shasradha/Orbit/hardware/Orbit-KiCad-Main/orbit.kicad_sch

## KiCad design hardware/Orbit-KiCad-Main/orbit.kicad_sch (2026-08-10)

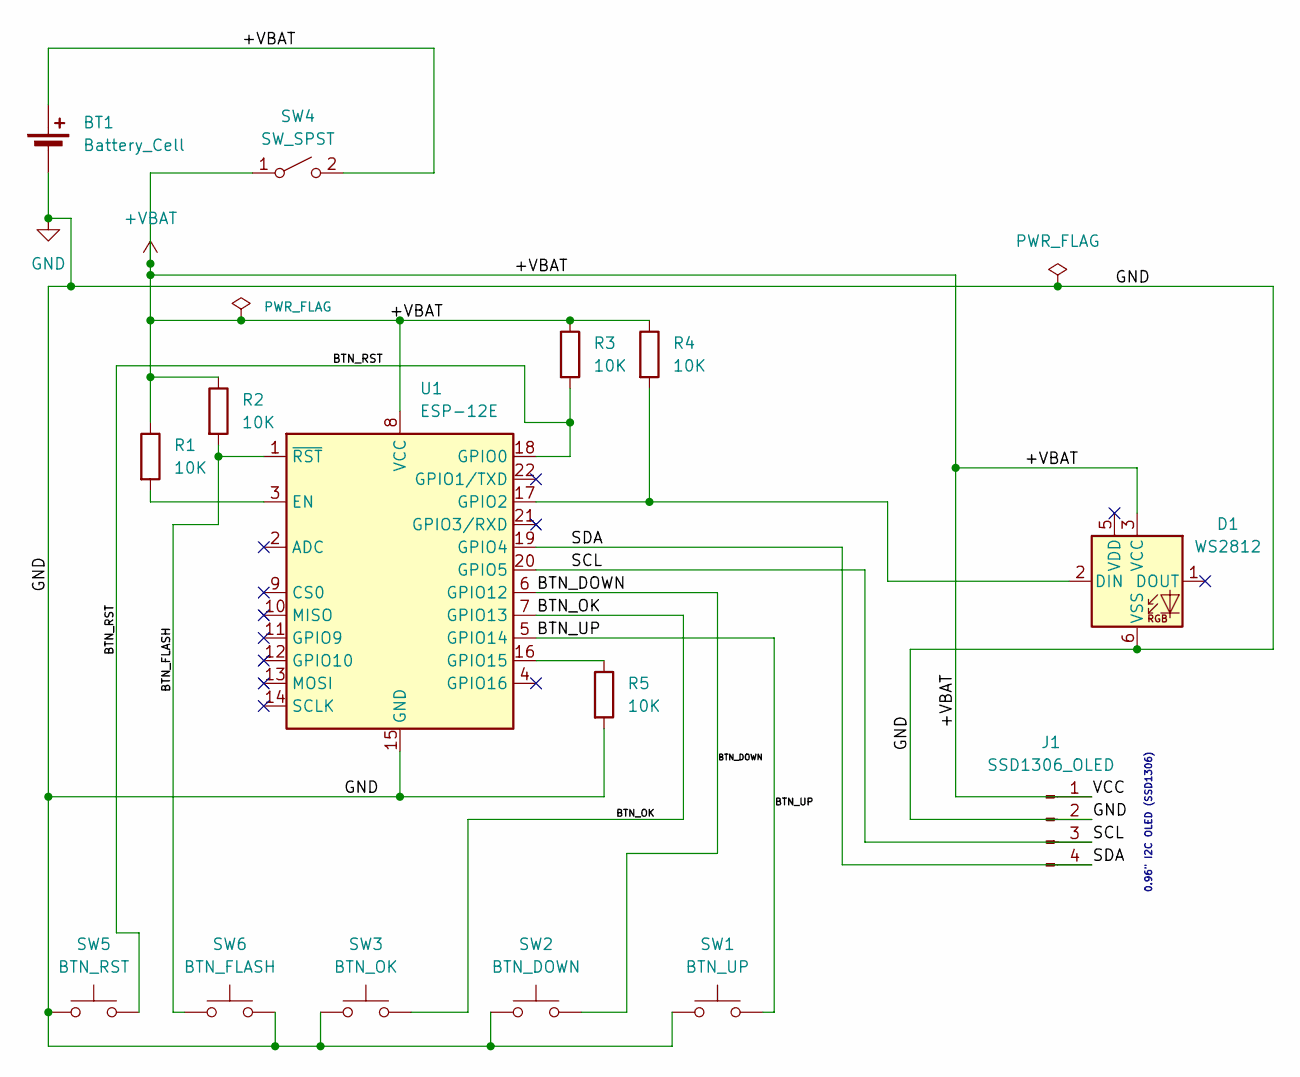
[picture p7: schematic orbit.kicad_sch]

Parts:
BT1: Battery_Cell
D1: WS2812; LED_WS2812_PLCC6_5.0x5.0mm_P1.6mm
J1: SSD1306_OLED
R1, R2, R3, R4, R5: 10K
SW1: BTN_UP
SW2: BTN_DOWN
SW3: BTN_OK
SW4: SW_SPST
SW5: BTN_RST
SW6: BTN_FLASH
U1: ESP-12E

Connections:
+VBAT: BT1.1 (+), D1.3 (VCC), J1.1, R1.1, R2.1, R3.1, R4.1, SW4.1 (A), SW4.2 (B), U1.8 (VCC)
BTN_DOWN: SW2.2, U1.6 (GPIO12)
BTN_FLASH: R2.2, SW6.1, U1.1 (~RST)
BTN_OK: SW3.2, U1.7 (GPIO13)
BTN_RST: R3.2, SW5.2, U1.18 (GPIO0)
BTN_UP: SW1.2, U1.5 (GPIO14)
GND: BT1.2 (-), D1.6 (VSS), J1.2, R5.2, SW1.1, SW2.1, SW3.1, SW5.1, SW6.2, U1.15 (GND)
unnamed: D1.2 (DIN), R4.2, U1.17 (GPIO2)
unnamed: R1.2, U1.3 (EN)
unnamed: R5.1, U1.16 (GPIO15)
SCL: J1.3, U1.20 (GPIO5)
SDA: J1.4, U1.19 (GPIO4)

Notes on the sheet:
0.96" I2C OLED (SSD1306)
