shasradha/Orbit/hardware/Orbit-Kicad-Flasher/orbit-flash-circuit/orbit-flash-circuit.kicad_sch

## KiCad design hardware/Orbit-Kicad-Flasher/orbit-flash-circuit/orbit-flash-circuit.kicad_sch (2026-08-10)

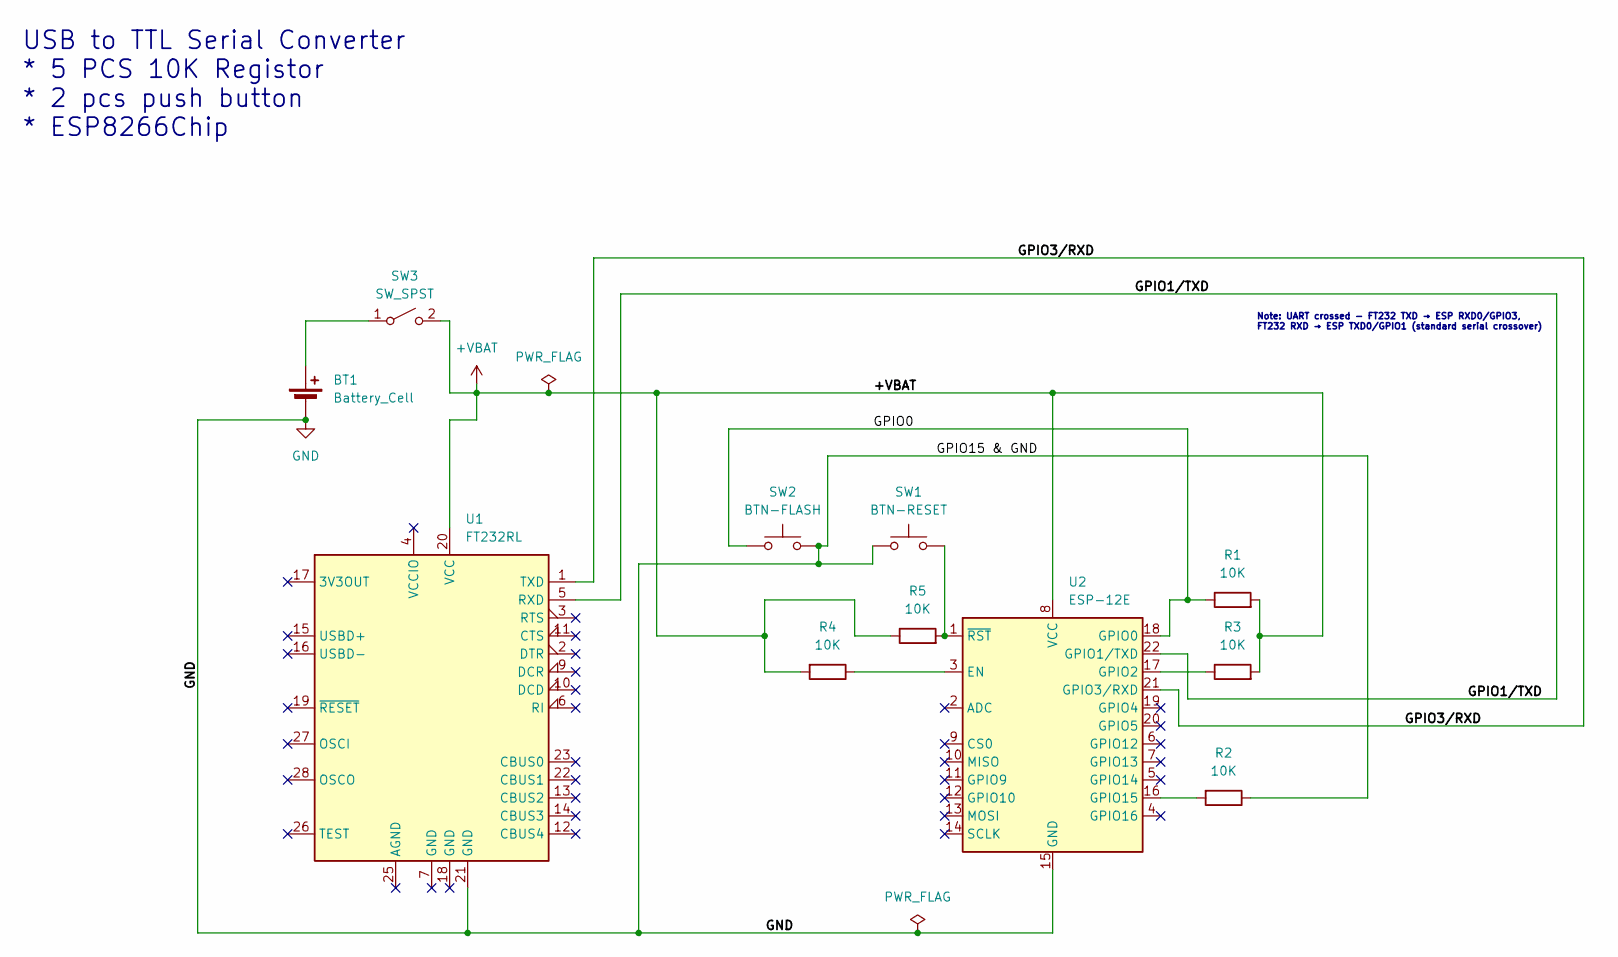
[picture p8: schematic orbit-flash-circuit.kicad_sch]

Parts:
BT1: Battery_Cell
R1, R2, R3, R4, R5: 10K
SW1: BTN-RESET
SW2: BTN-FLASH
SW3: SW_SPST
U1: FT232RL; SSOP-28_5.3x10.2mm_P0.65mm
U2: ESP-12E

Connections:
+VBAT: R1.2, R3.2, R4.2, R5.1, SW3.2 (B), U1.20 (VCC), U2.8 (VCC)
GND: BT1.2 (-), R2.1, SW1.1, SW2.2, U1.21 (GND), U2.15 (GND)
GPIO0: R1.1, SW2.1, U2.18 (GPIO0)
GPIO1/TXD: U1.5 (RXD), U2.22 (GPIO1/TXD)
GPIO3/RXD: U1.1 (TXD), U2.21 (GPIO3/RXD)
unnamed: BT1.1 (+), SW3.1 (A)
unnamed: R2.2, U2.16 (GPIO15)
unnamed: R3.1, U2.17 (GPIO2)
unnamed: R4.1, U2.3 (EN)
unnamed: R5.2, SW1.2, U2.1 (~RST)

Notes on the sheet:
USB to TTL Serial Converter * 5 PCS 10K Registor * 2 pcs push button * ESP8266Chip
Note: UART crossed - FT232 TXD → ESP RXD0/GPIO3, FT232 RXD → ESP TXD0/GPIO1 (standard serial crossover)
