shasradha/Orbit/firmware/Orbit-Firmware-Source/orbit_deauther/webfiles.h

/* This software is licensed under the MIT License: https://github.com/spacehuhntech/esp8266_deauther */

/* Modified for the Orbit hardware platform
   https://github.com/shasradha/Orbit
   Original firmware (c) spacehuhn, used under MIT License */

#ifndef webfiles_h
#define webfiles_h

// comment that out if you want to save program memory and know how to upload the web files to the SPIFFS manually
#define USE_PROGMEM_WEB_FILES 

#ifdef USE_PROGMEM_WEB_FILES
const char indexhtml[] PROGMEM = {0x1f, 0x8b, 0x08, 0x08, 0xb5, 0x3c, 0x14, 0x60, 0x02, 0xff, 0x69, 0x6e, 0x64, 0x65, 0x78, 0x2e, 0x68, 0x74, 0x6d, 0x6c, 0x00, 0x95, 0x55, 0x6d, 0x6f, 0xe3, 0x36, 0x0c, 0xfe, 0x2b, 0xac, 0xf7, 0x61, 0x1b, 0x10, 0xdb, 0x4d, 0x0b, 0x14, 0x5d, 0x11, 0x07, 0xd8, 0xd6, 0x76, 0x08, 0x76, 0x57, 0x1c, 0x76, 0xbd, 0xdd, 0xc7, 0x83, 0x2c, 0x31, 0xb1, 0x1a, 0x59, 0xf2, 0xf4, 0x92, 0x5c, 0x80, 0xfd, 0xf8, 0x91, 0xb2, 0xd3, 0xa6, 0x3d, 0x60, 0xd8, 0x80, 0xc0, 0xb1, 0x28, 0xf2, 0xd1, 0xc3, 0x87, 0x14, 0xbd, 0x38, 0x2b, 0xcb, 0x12, 0x1e, 0x3b, 0x1d, 0x20, 0xb8, 0x75, 0xdc, 0x0b, 0x8f, 0x40, 0xef, 0x46, 0x4b, 0xb4, 0x01, 0x15, 0x24, 0xab, 0xd0, 0x43, 0xec, 0x10, 0xde, 0xaf, 0x1e, 0xe1, 0xdd, 0x68, 0xbe, 0x81, 0x2e, 0xc6, 0x21, 0xdc, 0xd4, 0xf5, 0x46, 0xc7, 0x2e, 0xb5, 0x95, 0x74, 0x7d, 0x1d, 0x06, 0x21, 0xb1, 0x4b, 0x9d, 0x8d, 0x28, 0xbb, 0x1a, 0xc3, 0x70, 0x7d, 0x71, 0x75, 0xf5, 0x45, 0xa1, 0x48, 0x14, 0xed, 0xa1, 0x2c, 0x97, 0xb0, 0x38, 0xbb, 0x75, 0x32, 0x1e, 0x06, 0xa4, 0xf8, 0xde, 0xd0, 0xba, 0xc7, 0x28, 0x40, 0x76, 0xc2, 0x07, 0x8c, 0xcd, 0xa7, 0xc7, 0xfb, 0xf2, 0x1a, 0x8e, 0x56, 0x2b, 0x7a, 0x6c, 0x76, 0x1a, 0xf7, 0x83, 0xf3, 0x11, 0x40, 0x3a, 0xc2, 0xb5, 0xb1, 0x29, 0xf6, 0x5a, 0xc5, 0xae, 0x51, 0xb8, 0x23, 0x2a, 0x65, 0x5e, 0xcc, 0x40, 0x5b, 0x1d, 0xb5, 0x30, 0x65, 0x90, 0xc2, 0x60, 0x73, 0x5e, 0x5d, 0xcf, 0xa0, 0x27, 0x5b, 0x4f, 0xa6, 0xa4, 0x8b, 0x57, 0x88, 0xc4, 0xa5, 0xc7, 0x52, 0x3a, 0xe3, 0xfc, 0x09, 0xe8, 0x77, 0x97, 0x57, 0x97, 0x3f, 0x5d, 0x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
c1, 0xb6, 0x34, 0x50, 0xf5, 0x56, 0x67, 0x52, 0x7f, 0x3f, 0x43, 0x70, 0xc5, 0xc6, 0xdc, 0x97, 0xbf, 0x92, 0x50, 0x34, 0xd0, 0x26, 0xd6, 0x13, 0xb9, 0x7f, 0x00, 0x02, 0x19, 0x2a, 0x8c, 0xc3, 0x07, 0x00, 0x00};
const char scanhtml[] PROGMEM = {0x1f, 0x8b, 0x08, 0x08, 0xb5, 0x3c, 0x14, 0x60, 0x02, 0xff, 0x73, 0x63, 0x61, 0x6e, 0x2e, 0x68, 0x74, 0x6d, 0x6c, 0x00, 0xad, 0x57, 0x6d, 0x4f, 0xe3, 0x38, 0x10, 0xfe, 0x2b, 0x43, 0xef, 0x0b, 0x2b, 0xd1, 0xa6, 0x2d, 0x4b, 0x17, 0x50, 0x13, 0x89, 0x83, 0x5d, 0x09, 0x89, 0xdb, 0x45, 0x0b, 0x77, 0x27, 0xdd, 0x97, 0xca, 0x4d, 0xa6, 0x8d, 0x97, 0xd4, 0xae, 0x6c, 0xa7, 0x5d, 0xa4, 0xfb, 0xf1, 0xf7, 0xd8, 0x4e, 0x79, 0x49, 0x0b, 0x3a, 0xb4, 0x7c, 0x68, 0xea, 0x8c, 0x67, 0xc6, 0x33, 0x8f, 0xe7, 0x2d, 0xe3, 0xbd, 0x6e, 0xb7, 0x4b, 0xb7, 0xa5, 0xb4, 0x64, 0xf5, 0xcc, 0xad, 0x85, 0x61, 0xc2, 0xba, 0x92, 0x39, 0x2b, 0xcb, 0x05, 0xd5, 0xaa, 0x60, 0x43, 0xae, 0x64, 0xfa, 0xe3, 0xf2, 0x96, 0xae, 0x22, 0xf9, 0x94, 0x4a, 0xe7, 0x96, 0xf6, 0x34, 0x49, 0xe6, 0xd2, 0x95, 0xf5, 0xb4, 0x97, 0xeb, 0x45, 0x62, 0x97, 0x22, 0xe7, 0xb2, 0x2e, 0x95, 0xe3, 0xbc, 0x4c, 0xd8, 0x2e, 0x8f, 0x87, 0xa3, 0xd1, 0xa4, 0x60, 0x51, 0x43, 0xda, 0x50, 0xb7, 0x9b, 0xd1, 0x78, 0xef, 0x42, 0xe7, 0xee, 0x7e, 0xc9, 0x90, 0x5f, 0x54, 0x78, 0x5f, 0xb0, 0x13, 0x94, 0x97, 0xc2, 0x58, 0x76, 0xe9, 0x9f, 0xb7, 0x5f, 0xba, 0xc7, 0xb4, 0xa1, 0x2a, 0xb1, 0xe0, 0x74, 0x25, 0x79, 0xbd, 0xd4, 0xc6, 0x11, 0xe5, 0x1a, 0x7a, 0x95, 0x4b, 0x3b, 0x6b, 0x59, 0xb8, 0x32, 0x2d, 0x78, 0x05, 0x53, 0xba, 0xe1, 0xe5, 0x80, 0xa4, 0x92, 0x4e, 0x8a, 0xaa, 0x6b, 0x73, 0x51, 0x71, 0xda, 0xef, 0x1d, 0x1f, 0xd0, 0x02, 0xb4, 0x05, 0x48, 0xb5, 0xec, 0x3c, 0xd3, 0x08, 0x5b, 0x16, 0xdc, 0xcd, 0x75, 0xa5, 0xcd, 0x13, 0xa5, 0xb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
2, 0x23, 0x20, 0xe1, 0xf5, 0xc3, 0x34, 0x3c, 0xe8, 0xd2, 0x0f, 0x83, 0x01, 0xb0, 0xa6, 0xcc, 0x7c, 0x4c, 0xdc, 0xae, 0xeb, 0x52, 0xfd, 0x9a, 0x7d, 0xf9, 0xb5, 0x30, 0x06, 0x03, 0x30, 0xff, 0x1f, 0x21, 0x47, 0x45, 0xc3, 0xe3, 0x17, 0x2d, 0xdd, 0x47, 0x56, 0xef, 0x5b, 0xfd, 0xe3, 0xa2, 0x7d, 0xd5, 0x3e, 0xeb, 0xf2, 0x8c, 0xaa, 0xeb, 0xd8, 0x38, 0x1d, 0x7d, 0x51, 0xe4, 0x77, 0xd3, 0x6a, 0x7b, 0x25, 0x32, 0x57, 0x60, 0x5e, 0x8c, 0x2d, 0x57, 0xfc, 0x93, 0x02, 0xff, 0xa8, 0x9e, 0x94, 0x2f, 0xef, 0xff, 0xde, 0x43, 0xf0, 0x38, 0x56, 0xbd, 0xda, 0x0f, 0xaf, 0x63, 0x5f, 0xff, 0x6b, 0xe5, 0xfe, 0x03, 0x03, 0xc2, 0x59, 0xa3, 0x7f, 0x12, 0x00, 0x00};
const char ssidshtml[] PROGMEM = {0x1f, 0x8b, 0x08, 0x08, 0xb5, 0x3c, 0x14, 0x60, 0x02, 0xff, 0x73, 0x73, 0x69, 0x64, 0x73, 0x2e, 0x68, 0x74, 0x6d, 0x6c, 0x00, 0xb5, 0x57, 0xeb, 0x6f, 0xdb, 0x36, 0x10, 0xff, 0x57, 0xae, 0xde, 0x87, 0x6c, 0x40, 0x64, 0xe5, 0x01, 0x04, 0x59, 0x60, 0x09, 0x48, 0x9b, 0x14, 0x08, 0xd0, 0x47, 0xd0, 0x64, 0x2b, 0xf6, 0xc9, 0xa0, 0xa4, 0xb3, 0xc5, 0x9a, 0x22, 0x05, 0x92, 0xb2, 0x13, 0xa0, 0x7f, 0xfc, 0xee, 0x48, 0xc9, 0x71, 0x6c, 0x67, 0x68, 0xb7, 0xec, 0x8b, 0x4c, 0xde, 0x8b, 0xc7, 0x7b, 0xfc, 0x78, 0x9e, 0xbc, 0x49, 0x92, 0x04, 0xee, 0x6b, 0xe9, 0xc0, 0x99, 0x99, 0x5f, 0x09, 0x8b, 0x40, 0x6b, 0x25, 0x4b, 0xd4, 0x0e, 0x2b, 0xe8, 0x74, 0x85, 0x16, 0x7c, 0x8d, 0xf0, 0xf1, 0xe6, 0x1e, 0x3e, 0x44, 0xf2, 0x05, 0xd4, 0xde, 0xb7, 0xee, 0x22, 0x4d, 0xe7, 0xd2, 0xd7, 0x5d, 0x31, 0x2e, 0x4d, 0x93, 0xba, 0x56, 0x94, 0x58, 0x77, 0xb5, 0xf6, 0x58, 0xd6, 0x29, 0xba, 0xf6, 0xfc, 0xe4, 0xec, 0x6c, 0x5a, 0xa1, 0xe8, 0x48, 0xdb, 0x42, 0x92, 0xe4, 0x30, 0x79, 0x73, 0x65, 0x4a, 0xff, 0xd8, 0x22, 0xe9, 0x37, 0x8a, 0xf6, 0x0d, 0x7a, 0x01, 0x65, 0x2d, 0xac, 0x43, 0x9f, 0xfd, 0x71, 0xff, 0x3e, 0x39, 0x87, 0x81, 0xaa, 0x45, 0x83, 0xd9, 0x52, 0xe2, 0xaa, 0x35, 0xd6, 0x03, 0x94, 0x86, 0xec, 0x6a, 0x9f, 0x8d, 0x56, 0xb2, 0xf2, 0x75, 0x56, 0xe1, 0x92, 0x5c, 0x49, 0xc2, 0xe6, 0x10, 0xa4, 0x96, 0x5e, 0x0a, 0x95, 0xb8, 0x52, 0x28, 0xcc, 0x8e, 0xc6, 0xe7, 0x87, 0xd0, 0x10, 0xad, 0x21, 0x52, 0x27, 0x47, 0xcf, 0x2c, 0x92, 0x2f, 0x0d, 0x26, 0xa5, 0x51, 0xc6, 0x6e, 0x18, 0xfd, 0xe5, 0x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
xb4, 0xcd, 0xe0, 0xfe, 0x07, 0x53, 0x5d, 0xd3, 0x82, 0xe3, 0x0d, 0x00, 0x00};
const char settingshtml[] PROGMEM = {0x1f, 0x8b, 0x08, 0x08, 0xb5, 0x3c, 0x14, 0x60, 0x02, 0xff, 0x73, 0x65, 0x74, 0x74, 0x69, 0x6e, 0x67, 0x73, 0x2e, 0x68, 0x74, 0x6d, 0x6c, 0x00, 0x95, 0x55, 0x6d, 0x6f, 0xdb, 0x36, 0x10, 0xfe, 0x2b, 0x57, 0xed, 0x43, 0x12, 0x20, 0x92, 0x9a, 0x04, 0x08, 0xd2, 0x44, 0xd2, 0x30, 0x34, 0x0d, 0x10, 0x20, 0xdd, 0x8a, 0x26, 0xdb, 0x3e, 0x06, 0x34, 0x75, 0xb6, 0x58, 0x53, 0xa4, 0x46, 0x9e, 0xec, 0x06, 0xd8, 0x8f, 0xdf, 0x9d, 0x24, 0xe7, 0xc5, 0x71, 0x8a, 0xee, 0x83, 0x29, 0xfa, 0x78, 0x6f, 0xcf, 0xdd, 0xf1, 0x61, 0xf1, 0x2e, 0x4d, 0x53, 0xb8, 0x6b, 0x4c, 0x84, 0xe8, 0xe7, 0xb4, 0x56, 0x01, 0x81, 0xf7, 0xd6, 0x68, 0x74, 0x11, 0x6b, 0xe8, 0x5d, 0x8d, 0x01, 0xa8, 0x41, 0xf8, 0x7c, 0x7d, 0x07, 0x37, 0xa3, 0xf8, 0x1c, 0x1a, 0xa2, 0x2e, 0x9e, 0xe7, 0xf9, 0xc2, 0x50, 0xd3, 0xcf, 0x32, 0xed, 0xdb, 0x3c, 0x76, 0x4a, 0x63, 0xd3, 0x37, 0x8e, 0x50, 0x37, 0x39, 0xc6, 0xee, 0xec, 0xf8, 0xf4, 0xf4, 0xbe, 0x46, 0xd5, 0xb3, 0x75, 0x80, 0x34, 0xad, 0xa0, 0x78, 0x77, 0xe9, 0x35, 0x3d, 0x74, 0xc8, 0xf6, 0xad, 0xe5, 0xff, 0x2d, 0x92, 0x02, 0xdd, 0xa8, 0x10, 0x91, 0xca, 0x3f, 0xef, 0xae, 0xd2, 0x33, 0xd8, 0x48, 0x9d, 0x6a, 0xb1, 0x5c, 0x19, 0x5c, 0x77, 0x3e, 0x10, 0x80, 0xf6, 0xec, 0xd7, 0x51, 0x99, 0xac, 0x4d, 0x4d, 0x4d, 0x59, 0xe3, 0x8a, 0x53, 0x49, 0x87, 0x3f, 0x87, 0x60, 0x9c, 0x21, 0xa3, 0x6c, 0x1a, 0xb5, 0xb2, 0x58, 0xbe, 0xcf, 0xce, 0x0e, 0xa1, 0x65, 0x59, 0xcb, 0xa2, 0xde, 0x24, 0x2f, 0x3c, 0x72, 0x2e, 0x2d, 0xa6, 0xda, 0x5b, 0x1f, 0x9e, 0x39, 0xfd, 0xe5, 0xe4,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
, 0xba, 0xad, 0xc6, 0x62, 0x28, 0x48, 0x5e, 0xa8, 0x6b, 0xb3, 0x30, 0x97, 0xbf, 0xaa, 0x80, 0x7e, 0xde, 0x65, 0xa1, 0x11, 0xae, 0x08, 0x27, 0x10, 0xce, 0xec, 0x46, 0xde, 0x9e, 0xa0, 0x1f, 0xf4, 0xea, 0x19, 0x7e, 0x07, 0xf1, 0x63, 0x0c, 0xda, 0xc2, 0x0a, 0x00, 0x00};
const char sitejs[] PROGMEM = {0x1f, 0x8b, 0x08, 0x08, 0xb5, 0x3c, 0x14, 0x60, 0x02, 0xff, 0x73, 0x69, 0x74, 0x65, 0x2e, 0x6a, 0x73, 0x00, 0x9d, 0x56, 0x6d, 0x6f, 0xdb, 0x36, 0x10, 0xfe, 0x6c, 0xff, 0x8a, 0x9b, 0x0a, 0xd4, 0x52, 0xe2, 0x49, 0x46, 0xb2, 0x15, 0x5d, 0x1c, 0x77, 0x48, 0x8b, 0x74, 0x4d, 0xe1, 0xac, 0x40, 0xe2, 0x61, 0x03, 0x9a, 0x60, 0x60, 0xa4, 0x93, 0xad, 0x45, 0x26, 0x55, 0x92, 0x4a, 0x6a, 0xa4, 0xfe, 0xef, 0x3b, 0x92, 0x92, 0x2c, 0xd9, 0xde, 0xd6, 0xee, 0x43, 0x1c, 0x92, 0xcf, 0xdd, 0xf1, 0xf8, 0xdc, 0x9b, 0xa2, 0x03, 0x98, 0x2d, 0x32, 0x05, 0x4a, 0xa4, 0xfa, 0x91, 0x49, 0x04, 0x5a, 0xe7, 0x59, 0x8c, 0x5c, 0x61, 0x02, 0x25, 0x4f, 0x50, 0x82, 0x5e, 0x20, 0x5c, 0x5e, 0xcc, 0x60, 0xea, 0x8e, 0x4f, 0x60, 0xa1, 0x75, 0xa1, 0x4e, 0xa2, 0x68, 0x9e, 0xe9, 0x45, 0x79, 0x17, 0xc6, 0x62, 0x19, 0xa9, 0x82, 0xc5, 0xb8, 0x28, 0x17, 0x5c, 0x63, 0xbc, 0x88, 0x50, 0x15, 0x2f, 0x8f, 0x5e, 0xbc, 0xf8, 0x33, 0x41, 0x56, 0x92, 0xb6, 0x84, 0x83, 0xa8, 0xdf, 0x7f, 0x60, 0x12, 0x72, 0xc6, 0xe7, 0xef, 0x95, 0xe0, 0x30, 0x81, 0xa7, 0xf5, 0xb8, 0xdf, 0x4f, 0x4b, 0x1e, 0xeb, 0x8c, 0xf6, 0x73, 0xd4, 0xe7, 0x3e, 0x67, 0x4b, 0x0c, 0xe0, 0xa9, 0xdf, 0x93, 0xa8, 0x4b, 0xc9, 0x21, 0x11, 0x71, 0xb9, 0x44, 0xae, 0x43, 0x83, 0xe6, 0x68, 0x96, 0xaf, 0x57, 0x17, 0x89, 0x93, 0x1b, 0xf7, 0xd7, 0x2d, 0x7d, 0x54, 0xb1, 0xaf, 0xb4, 0xb4, 0xda, 0x59, 0x0a, 0xcd, 0xba, 0x36, 0x45, 0xfb, 0x50, 0x8b, 0x6b, 0x2d, 0x33, 0x3e, 0xf7, 0x03, 0x3a, 0xef, 0x85, 0x12, 0x8b, 0x9c, 0x9c, 0xf6, 0xa3, 0xe7, 0xd1, 0x7c,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
b, 0xd1, 0x4f, 0xcb, 0xdf, 0x28, 0x67, 0xda, 0xe0, 0x09, 0x55, 0xc5, 0xd7, 0xcd, 0x94, 0xc0, 0x91, 0x50, 0xab, 0xe6, 0x81, 0x49, 0xd5, 0x76, 0x86, 0xc6, 0xb0, 0x95, 0x33, 0xe8, 0x50, 0x12, 0xb9, 0xc5, 0x84, 0x74, 0xdc, 0xf5, 0x15, 0x1d, 0x36, 0xb7, 0x2e, 0x26, 0x06, 0x00, 0x00};
const char scanjs[] PROGMEM = {0x1f, 0x8b, 0x08, 0x08, 0xb5, 0x3c, 0x14, 0x60, 0x02, 0xff, 0x73, 0x63, 0x61, 0x6e, 0x2e, 0x6a, 0x73, 0x00, 0xcd, 0x5a, 0x7d, 0x4f, 0xe3, 0x46, 0x13, 0xff, 0x3b, 0xf9, 0x14, 0xdb, 0x54, 0xad, 0x93, 0x12, 0x12, 0x3b, 0x10, 0xae, 0x22, 0x90, 0x8a, 0xe3, 0xa8, 0x1e, 0x2a, 0xee, 0x45, 0x80, 0x1e, 0x3d, 0x2a, 0x8d, 0x90, 0x63, 0x2f, 0xd8, 0xc5, 0xb1, 0x23, 0xef, 0x06, 0x38, 0xb5, 0x7c, 0xf7, 0x67, 0x66, 0xd6, 0x76, 0xd6, 0xaf, 0x04, 0x7a, 0xd5, 0x9d, 0x84, 0x8c, 0xed, 0x99, 0x9d, 0x99, 0x9d, 0x9d, 0x99, 0xdf, 0xec, 0x3a, 0xc3, 0x9f, 0xd8, 0xa5, 0xe7, 0x0b, 0x26, 0xa2, 0x1b, 0xf9, 0x60, 0xc7, 0x9c, 0xc1, 0x7d, 0xe0, 0x3b, 0x3c, 0x14, 0xdc, 0x65, 0xab, 0xd0, 0xe5, 0x31, 0x93, 0x1e, 0x67, 0xef, 0x4f, 0x2f, 0xd9, 0x99, 0x7a, 0xbd, 0xcf, 0x3c, 0x29, 0x97, 0x62, 0x7f, 0x38, 0xbc, 0xf5, 0xa5, 0xb7, 0x9a, 0x0f, 0x9c, 0x68, 0x31, 0x14, 0x4b, 0xdb, 0xe1, 0xde, 0xca, 0x0b, 0x25, 0x77, 0xbc, 0x21, 0x17, 0xcb, 0x9f, 0x47, 0x7b, 0x7b, 0xd7, 0x2e, 0xb7, 0x57, 0x30, 0x3a, 0x66, 0x3f, 0x0d, 0xdb, 0xed, 0x7b, 0x3b, 0x66, 0xa1, 0xbd, 0xe0, 0xbf, 0x89, 0x28, 0x64, 0x87, 0xec, 0x6a, 0x36, 0xa1, 0x57, 0xc2, 0xb1, 0xc3, 0xe4, 0xd5, 0x5f, 0xcc, 0x06, 0xb9, 0x40, 0xe9, 0x33, 0x21, 0x6d, 0xe9, 0x47, 0x21, 0x3d, 0xb1, 0xa7, 0x49, 0xbb, 0x7d, 0xb3, 0x0a, 0x1d, 0x7c, 0xc3, 0xdc, 0xd8, 0x7e, 0xb8, 0x80, 0x31, 0xdd, 0x1e, 0xfb, 0xab, 0xdd, 0x42, 0x09, 0x9e, 0x5c, 0x04, 0x13, 0x75, 0x2b, 0x78, 0xc0, 0x1d, 0xc9, 0xdd, 0xe4, 0xf1, 0xc1, 0x77, 0xa5, 0x97, 0xdc, 0x3b, 0x51, 0x10, 0xc5,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
