shasradha/Orbit/firmware/Orbit-Firmware-Source/orbit_deauther/DisplayUI.h

/* This software is licensed under the MIT License: https://github.com/spacehuhntech/esp8266_deauther */

/* Modified for the Orbit hardware platform
   https://github.com/shasradha/Orbit
   Original firmware (c) spacehuhn, used under MIT License */
   
#pragma once

#include "language.h"
#include "A_config.h"
#include "Names.h"
#include "SSIDs.h"
#include "Scan.h"
#include "Attack.h"

// ===== adjustable ===== //
#if defined(SSD1306_I2C)
  #include <Wire.h>
  #include "src/esp8266-oled-ssd1306-4.1.0/SSD1306Wire.h"
#elif defined(SSD1306_SPI)
  #include <SPI.h>
  #include "src/esp8266-oled-ssd1306-4.1.0/SSD1306Spi.h"
#elif defined(SH1106_I2C)
  #include <Wire.h>
  #include "src/esp8266-oled-ssd1306-4.1.0/SH1106Wire.h"
#elif defined(SH1106_SPI)
  #include <SPI.h>
  #include "src/esp8266-oled-ssd1306-4.1.0/SH1106Spi.h"
#endif /* if defined(SSD1306_I2C) */

#ifdef RTC_DS3231
#include "src/DS3231-1.0.3/DS3231.h"
#endif // ifdef RTC_DS3231

#include "src/SimpleButton/SimpleButton.h"

using namespace simplebutton;


extern Names names;
extern SSIDs ssids;
extern Accesspoints accesspoints;
extern Stations     stations;
extern Scan     scan;
extern Attack   attack;
extern uint32_t currentTime;

extern String leftRight(String a, String b, int len);
extern String center(String a, int len);
extern String left(String a, int len);
extern String right(String a, int len);
extern String leftRight(String a, String b, int len);
extern String replaceUtf8(String str, String r);

const char D_INTRO_0[] PROGMEM = "Orbit";
const char D_INTRO_1[] PROGMEM = "by Shasradha";
const char D_INTRO_2[] PROGMEM = DISPLAY_TEXT;
const char D_RESETTING[] PROGMEM = "Resetting...";
const char D_SCANNING_0[] PROGMEM = "> Scanning";
const char D_SCANNING_1[] PROGMEM = "> Scanning.";
const char D_SCANNING_2[] PROGMEM = "> Scanning..";
const char D_SCANNING_3[] PROGMEM = "> Scanning...";

struct MenuNode {
    std::function<String()>getStr; // function used to create the displayed string
    std::function<void()>  click;  // function that is executed when node is clicked
    std::function<void()>  hold;   // function that is executed when node is pressed for > 800ms
};

struct Menu {
    SimpleList<MenuNode>* list;
    Menu                * parentMenu;
    uint8_t               selected;
    std::function<void()> build; // function that is executed when button is clicked
};

enum class DISPLAY_MODE { OFF,
                          BUTTON_TEST,
                          MENU,
                          LOADSCAN,
                          PACKETMONITOR,
                          INTRO,
                          CLOCK,
                          CLOCK_DISPLAY,
                          RESETTING };

class DisplayUI {
    public:
        DISPLAY_MODE mode = DISPLAY_MODE::MENU;
        bool highlightLED = false;

        Button* up   = NULL;
        Button* down = NULL;
        Button* a    = NULL;
        Button* b    = NULL;

        // ===== adjustable ===== //
#if defined(SSD1306_I2C)
        SSD1306Wire display = SSD1306Wire(I2C_ADDR, I2C_SDA, I2C_SCL);
#elif defined(SSD1306_SPI)
        SSD1306Spi display = SSD1306Spi(SPI_RES, SPI_DC, SPI_CS);
#elif defined(SH1106_I2C)
        SH1106Wire display = SH1106Wire(I2C_ADDR, I2C_SDA, I2C_SCL);
#elif defined(SH1106_SPI)
        SH1106Spi display = SH1106Spi(SPI_RES, SPI_DC, SPI_CS);
#endif /* if defined(SSD1306_I2C) */

        const uint8_t maxLen           = 18;
        const uint8_t lineHeight       = 12;
        const uint8_t buttonDelay      = 250;
        const uint8_t drawInterval     = 100; // 100ms = 10 FPS
        const uint16_t scrollSpeed     = 500; // time interval in ms
        const uint16_t screenIntroTime = 2500;
        const uint16_t screenWidth     = 128;
        const uint16_t sreenHeight     = 64;

        void configInit();
        void configOn();
        void configOff();
        void updatePrefix();
        void updateSuffix();
        void drawString(int x, int y, String str);
        void drawString(int row, String str);
        void drawLine(int x1, int y1, int x2, int y2);
        // ====================== //

        DisplayUI();
        ~DisplayUI();

        void setup();
#ifdef HIGHLIGHT_LED
        void setupLED();
#endif // ifdef HIGHLIGHT_LED

        void update(bool force = false);
        void on();
        void off();

    private:
        int16_t selectedID    = 0; // i.e. access point ID to draw the apMenu
        uint8_t scrollCounter = 0; // for horizontal scrolling

        uint32_t scrollTime = 0;   // last time a character was moved
        uint32_t drawTime   = 0;   // last time a frame was drawn
        uint32_t startTime  = 0;   // when the screen was enabled
        uint32_t buttonTime = 0;   // last time a button was pressed

        bool enabled = false;      // display enabled
        bool tempOff = false;

        // selected attack modes
        bool beaconSelected = false;
        bool deauthSelected = false;
        bool probeSelected  = false;

        // menus
        Menu* currentMenu;

        Menu mainMenu;

        Menu scanMenu;
        Menu showMenu;
        Menu attackMenu;
        Menu clockMenu;

        Menu apListMenu;
        Menu stationListMenu;
        Menu nameListMenu;
        Menu ssidListMenu;

        Menu apMenu;
        Menu stationMenu;
        Menu nameMenu;
        Menu ssidMenu;

        void setupButtons();

        String getChannel();

        // draw functions
        void draw(bool force = false);
        void drawButtonTest();
        void drawMenu();
        void drawLoadingScan();
        void drawPacketMonitor();
        void drawIntro();
        void drawResetting();
        void clearMenu(Menu* menu);

        // menu functions
        void changeMenu(Menu* menu);
        void goBack();
        void createMenu(Menu* menu, Menu* parent, std::function<void()>build);

        void addMenuNode(Menu* menu, std::function<String()>getStr, std::function<void()>click, std::function<void()>hold);
        void addMenuNode(Menu* menu, std::function<String()>getStr, std::function<void()>click);
        void addMenuNode(Menu* menu, std::function<String()>getStr, Menu* next);
        void addMenuNode(Menu* menu, const char* ptr, std::function<void()>click);
        void addMenuNode(Menu* menu, const char* ptr, Menu* next);

        // fake clock
        void drawClock();
        void setTime(int h, int m, int s);

        int clockHour   = 6;
        int clockMinute = 0;
        int clockSecond = 0;

        uint32_t clockTime = 0;

#ifdef RTC_DS3231
        DS3231 clock;
#endif // ifdef RTC_DS3231
};

// ===== FONT ===== //
// Created by http://oleddisplay.squix.ch/ Consider a donation
// In case of problems make sure that you are using the font file with the correct version!
const uint8_t DejaVu_Sans_Mono_12[] PROGMEM = {
    0x07,                                                                               // Width: 7
    0x0F,                                                                               // Height: 15
    0x20,                                                                               // First Char: 32
    0xE0,                                                                               // Numbers of Chars: 224

    // Jump Table:
    0xFF, 0xFF, 0x00, 0x07,                                                             // 32:65535
    0x00, 0x00, 0x08, 0x07,                                                             // 33:0
    0x00, 0x08, 0x09, 0x07,                                                             // 34:8
    0x00, 0x11, 0x0D, 0x07,                                                             // 35:17
    0x00, 0x1E, 0x0C, 0x07,                                                             // 36:30
    0x00, 0x2A, 0x0E, 0x07,                                                             // 37:42
    0x00, 0x38, 0x0E, 0x07,                                                             // 38:56
    0x00, 0x46, 0x07, 0x07,                                                             // 39:70
    0x00, 0x4D, 0x0C, 0x07,                                                             // 40:77
    0x00, 0x59, 0x0A, 0x07,                                                             // 41:89
    0x00, 0x63, 0x0B, 0x07,                                                             // 42:99
    0x00, 0x6E, 0x0E, 0x07,                                                             // 43:110
    0x00, 0x7C, 0x08, 0x07,                                                             // 44:124
    0x00, 0x84, 0x0A, 0x07,                                                             // 45:132
    0x00, 0x8E, 0x08, 0x07,                                                             // 46:142
    0x00, 0x96, 0x0D, 0x07,                                                             // 47:150
    0x00, 0xA3, 0x0E, 0x07,                                                             // 48:163
    0x00, 0xB1, 0x0C, 0x07,                                                             // 49:177
    0x00, 0xBD, 0x0E, 0x07,                                                             // 50:189
    0x00, 0xCB, 0x0E, 0x07,                                                             // 51:203
    0x00, 0xD9, 0x0E, 0x07,                                                             // 52:217
    0x00, 0xE7, 0x0E, 0x07,                                                             // 53:231
    0x00, 0xF5, 0x0E, 0x07,                                                             // 54:245
    0x01, 0x03, 0x0D, 0x07,                                                             // 55:259
    0x01, 0x10, 0x0E, 0x07,                                                             // 56:272
    0x01, 0x1E, 0x0E, 0x07,                                                             // 57:286
    0x01, 0x2C, 0x08, 0x07,                                                             // 58:300
    0x01, 0x34, 0x08, 0x07,                                                             // 59:308
    0x01, 0x3C, 0x0E, 0x07,                                                             // 60:316
    0x01, 0x4A, 0x0E, 0x07,                                                             // 61:330
    0x01, 0x58, 0x0E, 0x07,                                                             // 62:344
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
    0x00, 0x00, 0x80, 0x02, 0x80, 0x02, 0x80, 0x02, 0x80, 0x02, 0x80, 0x02, 0x80, 0x02, // 61
    0x00, 0x00, 0x20, 0x04, 0x40, 0x02, 0x40, 0x02, 0x40, 0x02, 0x80, 0x01, 0x80, 0x01, // 62
    0x00, 0x00, 0x00, 0x00, 0x10, 0x00, 0x88, 0x0D, 0xC8, 0x00, 0x48, 0x00, 0x30,       // 63
    0x00, 0x00, 0xC0, 0x0F, 0x20, 0x18, 0x10, 0x23, 0x90, 0x24, 0xB0, 0x24, 0xE0, 0x07, // 64
    0x00, 0x00, 0x00, 0x0C, 0xC0, 0x03, 0x38, 0x02, 0x38, 0x02, 0xC0, 0x03, 0x00, 0x0C, // 65
    0x00, 0x00, 0xF8, 0x0F, 0x88, 0x08, 0x88, 0x08, 0x88, 0x08, 0x88, 0x08, 0x70, 0x07, // 66
    0x00, 0x00, 0xE0, 0x03, 0x10, 0x04, 0x08, 0x08, 0x08, 0x08, 0x08, 0x08, 0x10, 0x04, // 67
    0x00, 0x00, 0xF8, 0x0F, 0x08, 0x08, 0x08, 0x08, 0x08, 0x08, 0x10, 0x04, 0xE0, 0x03, // 68
    0x00, 0x00, 0xF8, 0x0F, 0x88, 0x08, 0x88, 0x08, 0x88, 0x08, 0x88, 0x08, 0x88, 0x08, // 69
    0x00, 0x00, 0xF8, 0x0F, 0x88, 0x00, 0x88, 0x00, 0x88, 0x00, 0x88, 0x00, 0x88,       // 70
    0x00, 0x00, 0xE0, 0x03, 0x10, 0x04, 0x08, 0x08, 0x08, 0x08, 0x88, 0x08, 0x90, 0x07, // 71
    0x00, 0x00, 0xF8, 0x0F, 0x80, 0x00, 0x80, 0x00, 0x80, 0x00, 0x80, 0x00, 0xF8, 0x0F, // 72
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
};
